rlfbckr/nomidi/firmware/nomidi_firmware/inputs.ino

/*
  This file is part of
  NOMIDI - A OSC based performance controller

  Copyright (c) 2021 by Ralf Baecker <rlfbckr ~AT~ gmail.com>

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
  You should have received a copy of the GNU General Public License
  along with this program.  If not, see <http://www.gnu.org/licenses/>.
*/


void readInputs() {
  //  delayMicroseconds(20);
  for (int i = 0; i < 10 ; i++) {
    // int i = readinputtick % 10;
    // POT 0
    // POT0_RAW[i] = 1000; //(POT0_RAW[i] * (1.0 - inputValueSmoothing) + (mux_pot0.read(9 - i) - inputValueSmoothing));
    int tmp_pot0 = map(constrain((mux_pot0.read(9 - i) * inputValueGain), inputValueLowCut , inputValueHighCut), inputValueLowCut , inputValueHighCut, 0 , 4095);
    //  int tmp_pot0 = map(constrain((POT0_RAW[i] * inputValueGain), inputValueLowCut , inputValueHighCut), inputValueLowCut , inputValueHighCut, 0 , 4095);
    if (abs(tmp_pot0 - POT0_VALUES[i]) >= POT0_HYS[i]) {
      POT0_VALUES[i] = tmp_pot0;
      if (POT0_HYS[i] > inputHysteresisMin) {
        POT0_HYS[i]--;
        POT0_HYS_LAST_CHANGE[i] = millis();
      }
    }
    if ((millis() - POT0_HYS_LAST_CHANGE[i]) > inputHysteresisIntervall) {
      if (POT0_HYS[i] < inputHysteresisMax) {
        POT0_HYS[i]++;
      }
    }
  }

  delayMicroseconds(20);
  for (int i = 0; i < 10 ; i++) {
    // POT 1
    POT1_RAW[i] = (POT1_RAW[i] * (1.0 - inputValueSmoothing) + (mux_pot1.read(9 - i) - inputValueSmoothing));
    int tmp_pot1 = map(constrain((POT1_RAW[i] * inputValueGain), inputValueLowCut , inputValueHighCut), inputValueLowCut , inputValueHighCut, 0 , 4095);

    //  int tmp_pot1 = map(constrain((mux_pot1.read(9 - i) * inputValueGain), inputValueLowCut , inputValueHighCut), inputValueLowCut , inputValueHighCut, 0 , 4095);
    if (abs(tmp_pot1 - POT0_VALUES[i]) >= POT1_HYS[i]) {
      POT1_VALUES[i] = tmp_pot1;
      if (POT0_HYS[i] > inputHysteresisMin) {
        POT1_HYS[i]--;
        POT1_HYS_LAST_CHANGE[i] = millis();
      }
    }
    if ((millis() - POT1_HYS_LAST_CHANGE[i]) > inputHysteresisIntervall) {
      if (POT1_HYS[i] < inputHysteresisMax) {
        POT1_HYS[i]++;
      }
    }
  }
  delayMicroseconds(20);
  for (int i = 0; i < 10 ; i++) {
    // FADER
    int tmp_fader = map(constrain((mux_fader.read(9 - i) * inputValueGain), inputValueLowCut , inputValueHighCut), inputValueLowCut , inputValueHighCut, 0 , 4095);
    if (abs(tmp_fader - FADER_VALUES[i]) >= FADER_HYS[i]) {
      FADER_VALUES[i] = tmp_fader;
      if (FADER_HYS[i] > inputHysteresisMin) {
        FADER_HYS[i]--;
        FADER_HYS_LAST_CHANGE[i] = millis();
      }
    }
    if ((millis() - FADER_HYS_LAST_CHANGE[i]) > inputHysteresisIntervall) {
      if (FADER_HYS[i] < inputHysteresisMax) {
        FADER_HYS[i]++;
      }
    }

  }
  // Serial.println();
  delayMicroseconds(10);

  for (int i = 0; i < 10 ; i++) {
    BUTTON1_VALUES_LAST[i] = BUTTON1_VALUES[i];
    BUTTON0_VALUES_LAST[i] = BUTTON0_VALUES[i];
    if (mux_button0.read(9 - i) > 10) {
      BUTTON0_VALUES[i] = 1;
    } else {
      BUTTON0_VALUES[i] = 0;
    }

    if (mux_button1.read(9 - i) > 10) {
      BUTTON1_VALUES[i] = 1;
    } else {
      BUTTON1_VALUES[i] = 0;
    }

    if (BUTTON0_VALUES_LAST[i] == 0 && BUTTON0_VALUES[i] == 1) {
      BUTTON0_PUSHTIME_START[i] = millis();
    }

    if (BUTTON1_VALUES_LAST[i] == 0 && BUTTON1_VALUES[i] == 1) {
      BUTTON1_PUSHTIME_START[i] = millis();
    }

    if (BUTTON0_VALUES_LAST[i] == 1 && BUTTON0_VALUES[i] == 0) {
      Serial.print("BUTTON0_PUSHTIME[");
      Serial.print( i );
      Serial.print("] = ");
      BUTTON0_PUSHTIME[i] = millis() - BUTTON0_PUSHTIME_START[i];
      Serial.println(BUTTON0_PUSHTIME[i]);
    }

    if (BUTTON1_VALUES_LAST[i] == 1 && BUTTON1_VALUES[i] == 0) {
      Serial.print("BUTTON1_PUSHTIME[");
      Serial.print( i );
      Serial.print("] = ");
      BUTTON1_PUSHTIME[i] = millis() - BUTTON1_PUSHTIME_START[i];
      Serial.println(BUTTON1_PUSHTIME[i]);
    }
  }

  if (BUTTON0_PUSHTIME[0] > 2000 && BUTTON0_PUSHTIME[9] > 2000) {
    //  Serial.println(" C O N F I G   M*O*D*E !!!");
    BUTTON0_PUSHTIME[0] = 0;
    BUTTON0_PUSHTIME[9] = 0;
    _SETUPMODE_ = !_SETUPMODE_;
    if (!_SETUPMODE_) {
      sprintf(segmentData, "- NOMIDI -");
    }
  }
  if (BUTTON0_PUSHTIME[1] > 10) {
    //  Serial.println("BUTTON_SWI !!!");
    BUTTON0_PUSHTIME[1] = 0;
    BUTTON_SWI = true;
  }
  if (BUTTON0_PUSHTIME[2] > 10) {
    //  Serial.println("BUTTON_PRE !!!");
    BUTTON0_PUSHTIME[2] = 0;
    BUTTON_PRE = true;
  }
  if (BUTTON0_PUSHTIME[3] > 10) {
    // Serial.println("BUTTON_NXT !!!");
    BUTTON0_PUSHTIME[3] = 0;
    BUTTON_NXT = true;
  }
  if (BUTTON0_PUSHTIME[4] > 10) {
    //   Serial.println("BUTTON_SEL !!!");
    BUTTON0_PUSHTIME[4] = 0;
    BUTTON_SEL = true;
  }

  delayMicroseconds(10);
}
