rlfbckr/nomidi/firmware/nomidi_firmware/osc.ino

/*
  This file is part of
  NOMIDI - A OSC based performance controller

  Copyright (c) 2021 by Ralf Baecker <rlfbckr ~AT~ gmail.com>

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
  You should have received a copy of the GNU General Public License
  along with this program.  If not, see <http://www.gnu.org/licenses/>.
*/

void OSCsetLED(OSCMessage &msg, int addrOffset) {
#ifdef DEBUG_OSC_MSG
  Serial.print("> /nm/setLED ");
#endif
  int pos = msg.getInt(0);
  int intensity = msg.getInt(1);
  if (pos >= 0 && pos < 10) {
#ifdef DEBUG_OSC_MSG
    Serial.print(pos);
    Serial.print(" ");
    Serial.println(intensity);
#endif
    ledIntesity[pos] = intensity;
  }
}

void OSCset7Seg(OSCMessage &msg, int addrOffset) {
#ifdef DEBUG_OSC_MSG
  Serial.print("> /nm/set7seg ");
#endif
  int pos = msg.getInt(0);
  char letter = (char) msg.getInt(1);
  if (pos >= 0 && pos < 10) {
#ifdef DEBUG_OSC_MSG
    Serial.print(pos);
    Serial.print(" ");
    Serial.println(letter);
#endif
    segmentData[pos] = letter;
  }
}

void OSCset7SegAll(OSCMessage &msg, int addrOffset) {
  int pos = msg.getInt(0);
  char letter = (char) msg.getInt(1);
  for (int i = 0; i < 10; i++) {
    segmentData[i] = (char) msg.getInt(i);
  }
}

void sendInputsOSC() {
  OSCBundle bndl  ;
  for (int i = 0; i < 10; i++) {
    if (FADER_VALUES[i] != FADER_VALUES_LAST[i]) {
      bndl.add("/nm/f").add((int) i).add((int) FADER_VALUES[i]);
      FADER_VALUES_LAST[i] = FADER_VALUES[i];
    }
    if (POT0_VALUES[i] != POT0_VALUES_LAST[i]) {
      bndl.add("/nm/p0").add((int) i).add((int) POT0_VALUES[i]);
      POT0_VALUES_LAST[i] = POT0_VALUES[i];
    }
    if (POT1_VALUES[i] != POT1_VALUES_LAST[i]) {
      bndl.add("/nm/p1").add((int) i).add((int) POT1_VALUES[i]);
      POT1_VALUES_LAST[i] = POT1_VALUES[i];
    }
    if (BUTTON0_VALUES[i] != BUTTON0_VALUES_LAST_SEND[i]) {
      bndl.add("/nm/b0").add((int) i).add((int) BUTTON0_VALUES[i]);
      BUTTON0_VALUES_LAST_SEND[i] = BUTTON0_VALUES[i];
    }
    if (BUTTON1_VALUES[i] != BUTTON1_VALUES_LAST_SEND[i]) {
      bndl.add("/nm/b1").add((int) i).add((int) BUTTON1_VALUES[i]);
      BUTTON1_VALUES_LAST_SEND[i] = BUTTON1_VALUES[i];
    }
  }
#ifdef USE_SLIP_SERIAL
  SLIPSerial.beginPacket();
  bndl.send(SLIPSerial);
  SLIPSerial.endPacket();
#endif
#ifdef USE_ETHERNET
  Udp.beginPacket(serverIP, serverPort);
  bndl.send(Udp);
  Udp.endPacket();
#endif
  bndl.empty();

}
