rlfbckr/nomidi/firmware/nomidi_firmware/animation.h

boolean animation = true;
int animation_speed = 20;
int animation_frame = 0;
int animation_last_frame = 0;
int animation_length = 74;


char animation_data[][10] = {
  "          ",
  "-         ",
  "--        ",
  "---       ",
  "----      ",
  "-----     ",
  "------    ",
  "-------   ",
  "--------  ",
  "--------- ",
  "----------",
  "I---------",
  "DI--------",
  "IDI-------",
  "MIDI------",
  "OMIDI-----",
  "NOMIDI----",
  "-NOMIDI---",
  "--NOMIDI--",
  "--NOMIDI--",
  "--NOMIDI--",
  "--NOMIDI--",
  "--NOMIDI--",
  "--NOMIDI--",
  "--NOMIDI--",
  "--NOMIDI--",

  "--NOMIDI--",
  "---OMID---",
  "----MI----",
  "----------",
  "----------",
  "----__----",
  "---____---",
  "--______--",
  "-________-",
  "__________",
  "-________-",
  "--______--",
  "---____---",
  "----__----",
  "----------",
  "----------",
  "----^^----",
  "---^^^^---",
  "--^^^^^^--",
  "-^^^^^^^^-",
  "^^^^^^^^^^",
  "^^^^--^^^^",
  "^^^----^^^",
  "^^------^^",
  "^--------^",
  "----------",
  "----------",
  "_---------",
  "__--------",
  "___-------",
  "____------",
  "_____-----",
  "______----",
  "_______---",
  "________--",
  "_________-",
  "__________",
  "_________-",
  "________-^",
  "_______-^^",
  "______-^^ ",
  "_____-^^  ",
  "____-^^   ",
  "___-^^    ",
  "__-^^     ",
  "_-^^      ",
  "-^^       ",
  "^^        ",
  "^         ",

  "^^        ",
  " ^^       ",
  "  ^^      ",
  "   ^^     ",
  "    ^^    ",
  "     ^^   ",
  "      ^^  ",
  "       ^^ ",
  "        ^^",
  "         ^",
  "         \\",
  "         i",
  "         /",
  "        __",
  "       __ ",
  "      __  ",
  "     __   ",
  "    __    ",
  "   __     ",
  "  __      ",
  " __       ",
  "__        ",
  ",         ",
  "|         ",
  "#         ",
  "^^        ",
  " ^^       ",
  "  ^^      ",
  "   ^^     ",
  "    ^^    ",
  "     ^^   ",
  "      ^^  ",
  "       ^^ ",
  "        ^^",
  "         ^",
  "         \\",
  "         i",
  "         /",
  "        __",
  "       __ ",
  "      __  ",
  "     __   ",
  "    __    ",
  "   __     ",
  "  __      ",
  " __       ",
  "__        ",
  ",         ",
  "|         ",
  "#         ",
  "          ",
  "-         ",
  " -        ",
  "I -       ",
  "DI -      ",
  "IDI -     ",
  "OMIDI -   ",
  "NOMIDI -  ",
  " NOMIDI - ",
  "- NOMIDI -",
  "-        -",
  "- NOMIDI -",

};
